luftaquila/fsk-timekeeper/device/firmware/src/mac_master.h

/* Master MAC (DESIGN §2.8): a beacon every BEACON_PERIOD_MS on the TIMER1
 * grid with the slot table and cumulative ACKs, then receive-only through the
 * slots. Checks transport integrity only (authentication, session, replay,
 * order); judging the evidence is the console's job. Main-loop context. */
#ifndef MAC_MASTER_H
#define MAC_MASTER_H

#include <stdint.h>

#include "master_queue.h"
#include "registry.h"

typedef struct {
    registry_t reg;
    mq_t *q;
    uint64_t next_beacon;  /* TIMER1 tick of the next beacon start */
    uint8_t  seq;
    int      m_tx_valid;
    uint64_t m_tx_last;    /* TxDone of the last beacon */
    uint8_t  cp_id;
    unsigned cp_left;
    uint32_t auth_drop;    /* AEAD failures (not attributable to a sensor) */
    uint32_t ver_drop;     /* packets of another radio protocol version */
    uint32_t reset_after_ms;
    uint32_t reset_backoff_ms;
} mac_master_t;

void mac_master_init(mac_master_t *m, mq_t *q);

/* One main-loop pass; returns 1 when a beacon went out. */
int mac_master_step(mac_master_t *m);

/* Host `CP`: the next CP_REQ_BEACONS beacons ask every sensor for a checkpoint. */
void mac_master_checkpoint(mac_master_t *m);

/* A new master session after sec_init(). */
void mac_master_session(mac_master_t *m);

/* D line for every registered sensor (`?STATUS`), or only for those whose link
 * state changed (once per beacon). */
void mac_master_report(mac_master_t *m, int changed_only);

#endif /* MAC_MASTER_H */
